Emile666/stc1000_stm8/img/M05 connector-2.jpg

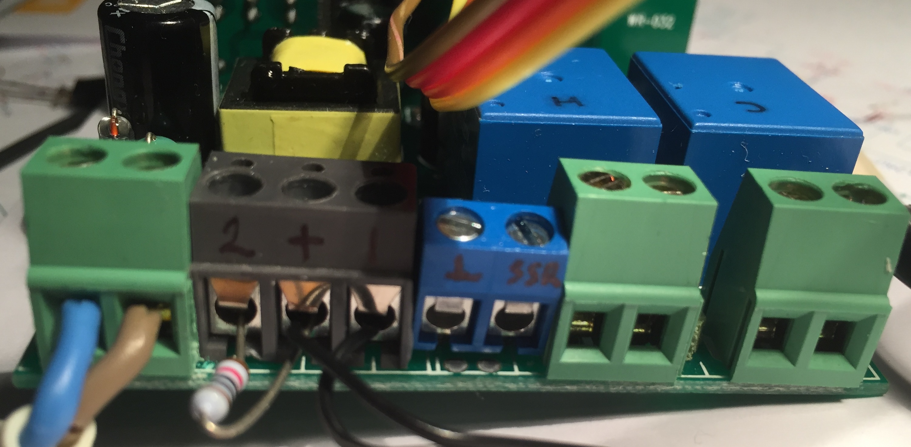
img/M05 connector-2.jpg
